yuanyong2024/picoduino/pictures/3.jpg

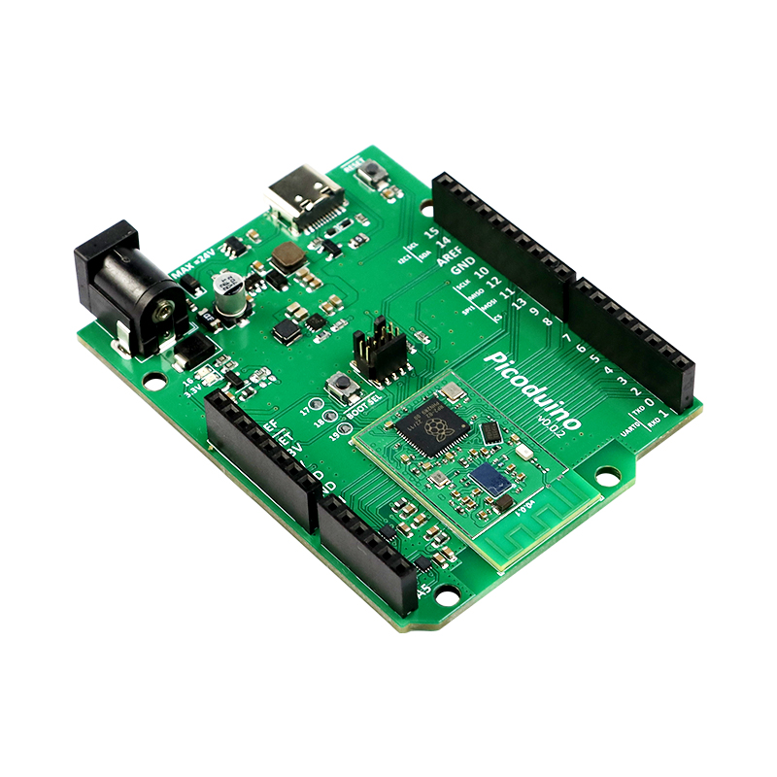
pictures/3.jpg
