yuanyong2024/picoduino/pictures/4.jpg

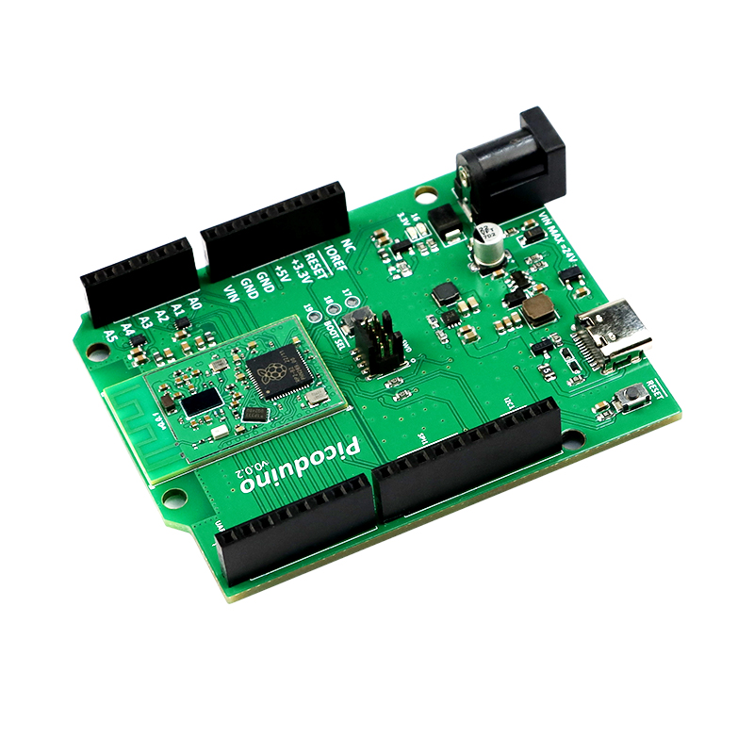
pictures/4.jpg
